cpldcpu/Nanite/Nanite841/Nanite-841_circuit.PNG

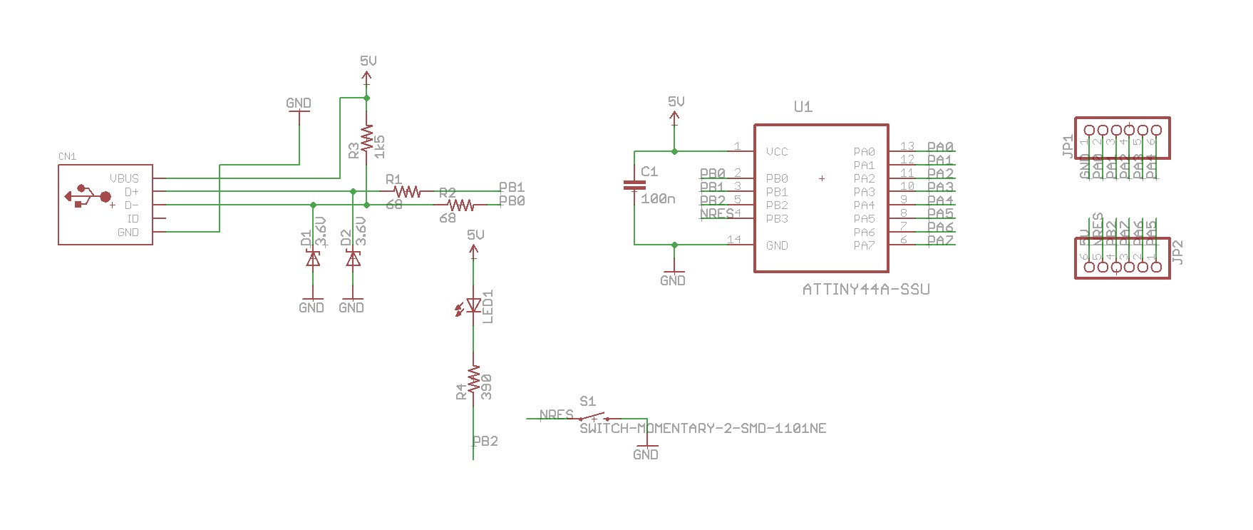
Nanite841/Nanite-841_circuit.PNG
